rzetelnyStudent/Bluetooth-bike-tire-pressure-sensor/Bluetooth bike tire pressure sensor/Software/Source/BLE TPMS V1/pca10040/s132/ses/Ble_buffer.h

#ifndef BLE_BUFFER_H
#define BLE_BUFFER_H

#include "my_config.h"
#include "nrf_sdh_ble.h"
#include <stdbool.h>
#include <stdint.h>

/* Class wrapping ble buffer. nrf SDK requires switching buffers to update advertising. This class does this. 
 * Everytime getBuffer() is called internal buffer is switched for the next update. 
 */
class Ble_buffer
{

    const uint8_t PRESS_POS = 17;	  // index of bytes representing pressure in advertising buffer
    const uint8_t TEMP_POS = 21;
    const uint8_t BAT_POS = 25;
    const uint8_t LEAK_FLAG_POS = 26;
    bool use_buffer1;      // bool used to toggle between buffers.
    uint8_t my_adv_data_1[cfg::ADV_DATA_L];      // advertising data buffer 1.
    uint8_t my_scan_data_1[cfg::SCAN_DATA_L];    // scan response data buffer 1. 
    uint8_t my_adv_data_2[cfg::ADV_DATA_L];      // advertising data buffer 2.
    uint8_t my_scan_data_2[cfg::SCAN_DATA_L];    // scan response data buffer 2. 
    ble_gap_adv_data_t ble_adv_struct_1;
    ble_gap_adv_data_t ble_adv_struct_2;

    void setPressure(uint32_t p_pressure);
    void setTemp(int32_t p_temp);
    void setBat(uint8_t p_temp);
    void setLeakFlag(bool p_leak);

  public:
    Ble_buffer();
    ble_gap_adv_data_t *getBuffer();
    void setPressTempLeak(const uint32_t p_pressure, const int32_t p_temperature, const uint8_t p_bat_percentage, const bool p_leak);
};

#endif
