rzetelnyStudent/Bluetooth-bike-tire-pressure-sensor/Bluetooth bike tire pressure sensor/Software/Source/BLE TPMS V1/pca10040/s132/ses/nrf_files.h

#ifndef NRF_FILES_H
#define NRF_FILES_H


extern "C" 
{
#include <stdbool.h>
#include <stdint.h>

#include "nordic_common.h"
#include "nrf.h"
#include "app_error.h"
#include "ble.h"
//#include "ble_hci.h"
//#include "ble_srv_common.h"
//#include "ble_advertising.h"
//#include "ble_conn_params.h"
#include "nrf_sdh.h"
#include "nrf_sdh_soc.h"
#include "nrf_sdh_ble.h"
#include "fds.h"
//#include "ble_conn_state.h"
//#include "nrf_ble_gatt.h"
//#include "nrf_ble_qwr.h"
#include "nrf_pwr_mgmt.h"
}

#endif
